jonscrp/Air-Quality-Sensor/CSL-AQS-V4/arduino_secrets.h

#define SECRET_SSID "NGENSMOTO"
#define SECRET_PASS "N63n5adm1n" 

// Google Sheets Script Deployment IDs GSSD_ID
// e.g AKfycbzLiMdE-5IlsuSrTyAcxUdH3eCu7B1Sl_mVJF2-Tge5Y8Zv66d9 from the Google Sheets Script Deployment ID
#define GSSD_ID "AKfycbzF5_BDwYa4JDZlBUvKoEfIe6r9hTPPPTD9T_ycSO_72WMTdRWt0Mhb8IISrDaQy76uWA"
