jonscrp/Air-Quality-Sensor/CSL-AQS-V4/sen5x.ino

String readSen5x(){
    uint16_t error;
    char errorMessage[256];

    delay(1000);

    // Read Measurement
    float massConcentrationPm1p0;
    float massConcentrationPm2p5;
    float massConcentrationPm4p0;
    float massConcentrationPm10p0;
    float ambientHumidity;
    float ambientTemperature;
    float vocIndex;
    float noxIndex;

    error = sen5x.readMeasuredValues(
        massConcentrationPm1p0, massConcentrationPm2p5, massConcentrationPm4p0,
        massConcentrationPm10p0, ambientHumidity, ambientTemperature, vocIndex,
        noxIndex);

    if (error) {
        Serial.print("Error trying to execute readMeasuredValues(): ");
        errorToString(error, errorMessage, 256);
        Serial.println(errorMessage);
    }

    String sen5xString = String(massConcentrationPm1p0) + String(", ") + String(massConcentrationPm2p5) + String(", ") + String(massConcentrationPm4p0) + String(", ") 
    + String(massConcentrationPm10p0) + String(", ") + String(ambientHumidity) + String(", ") + String(ambientTemperature) + String(", ") + String(vocIndex) + String(", ")
    + String(noxIndex)+ String(", ");
    Pmv = massConcentrationPm2p5;
    Voc = vocIndex;
    Nox = noxIndex;
  return sen5xString;
}

void initializeSen5x(){
  Serial.print("starting Sen5x... ");
    Serial.begin(115200);
    
    while (!Serial) {
        delay(100);
    }

    Wire.begin();

    sen5x.begin(Wire);

    uint16_t error;
    char errorMessage[256];
    error = sen5x.deviceReset();
    if (error) {
        Serial.print("Error trying to execute deviceReset(): ");
        errorToString(error, errorMessage, 256);
        Serial.println(errorMessage);
    }

    float tempOffset = 0.0;
    error = sen5x.setTemperatureOffsetSimple(tempOffset);
    if (error) {
        Serial.print("Error trying to execute setTemperatureOffsetSimple(): ");
        errorToString(error, errorMessage, 256);
        Serial.println(errorMessage);
    } else {
        Serial.print("Temperature Offset set to ");
        Serial.print(tempOffset);
        Serial.println(" deg. Celsius (SEN54/SEN55 only");
    }

    // Start Measurement
    error = sen5x.startMeasurement();
    if (error) {
        Serial.print("Error trying to execute startMeasurement(): ");
        errorToString(error, errorMessage, 256);
        Serial.println(errorMessage);
    }

}
